anarion80/porcupine/images/porcupine_4thumb_keys_bottom_plate-back.png

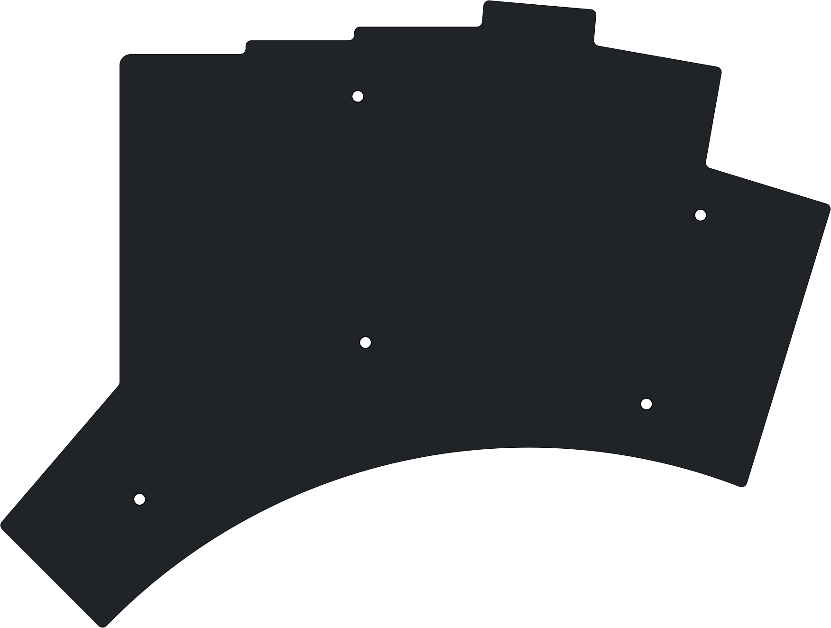
images/porcupine_4thumb_keys_bottom_plate-back.png
