anarion80/porcupine/images/porcupine_6x3_bottom_plate-back.png

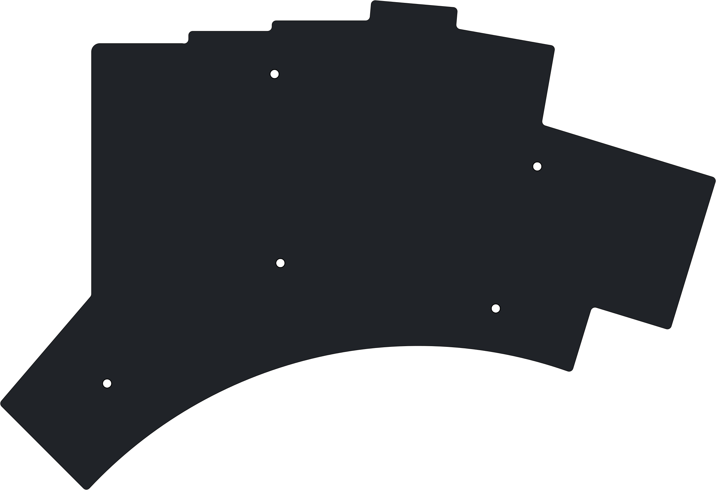
images/porcupine_6x3_bottom_plate-back.png
