anarion80/porcupine/images/porcupine_6x3_top_plate-back.png

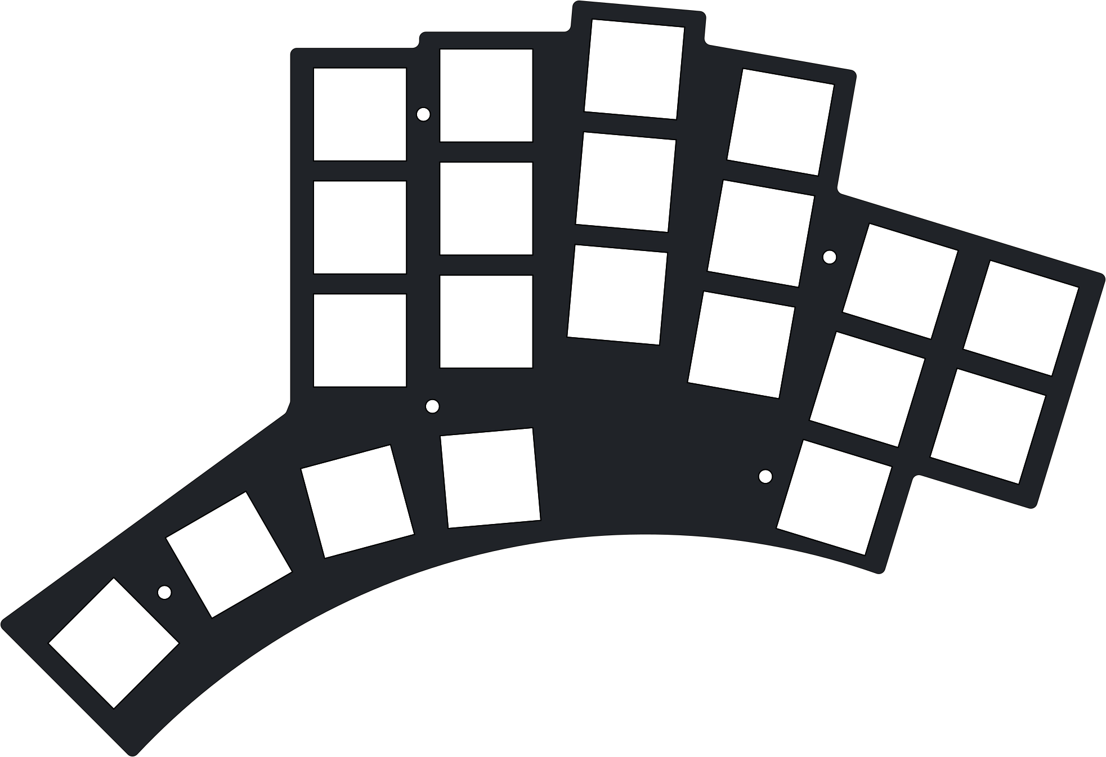
images/porcupine_6x3_top_plate-back.png
