anarion80/porcupine/images/porcupine_bottom_plate-back.png

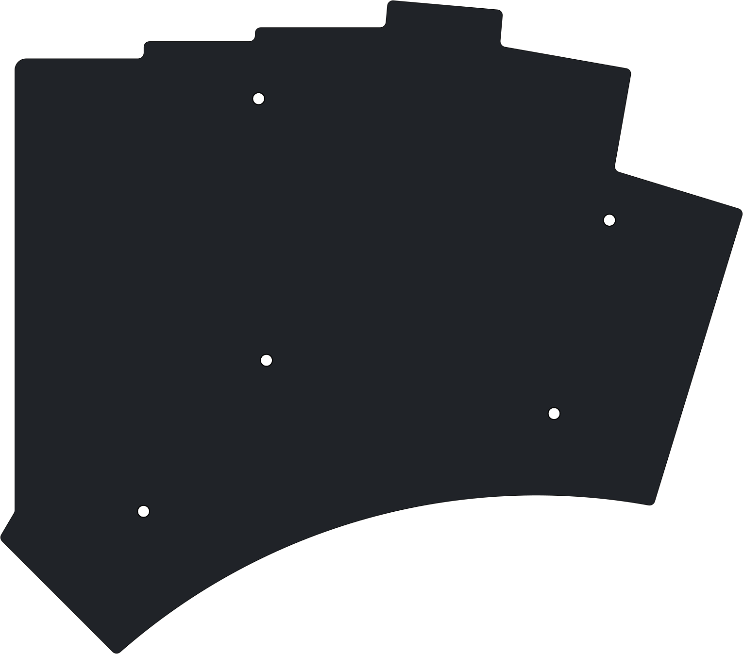
images/porcupine_bottom_plate-back.png
