anarion80/porcupine/images/porcupine_routed-front.png

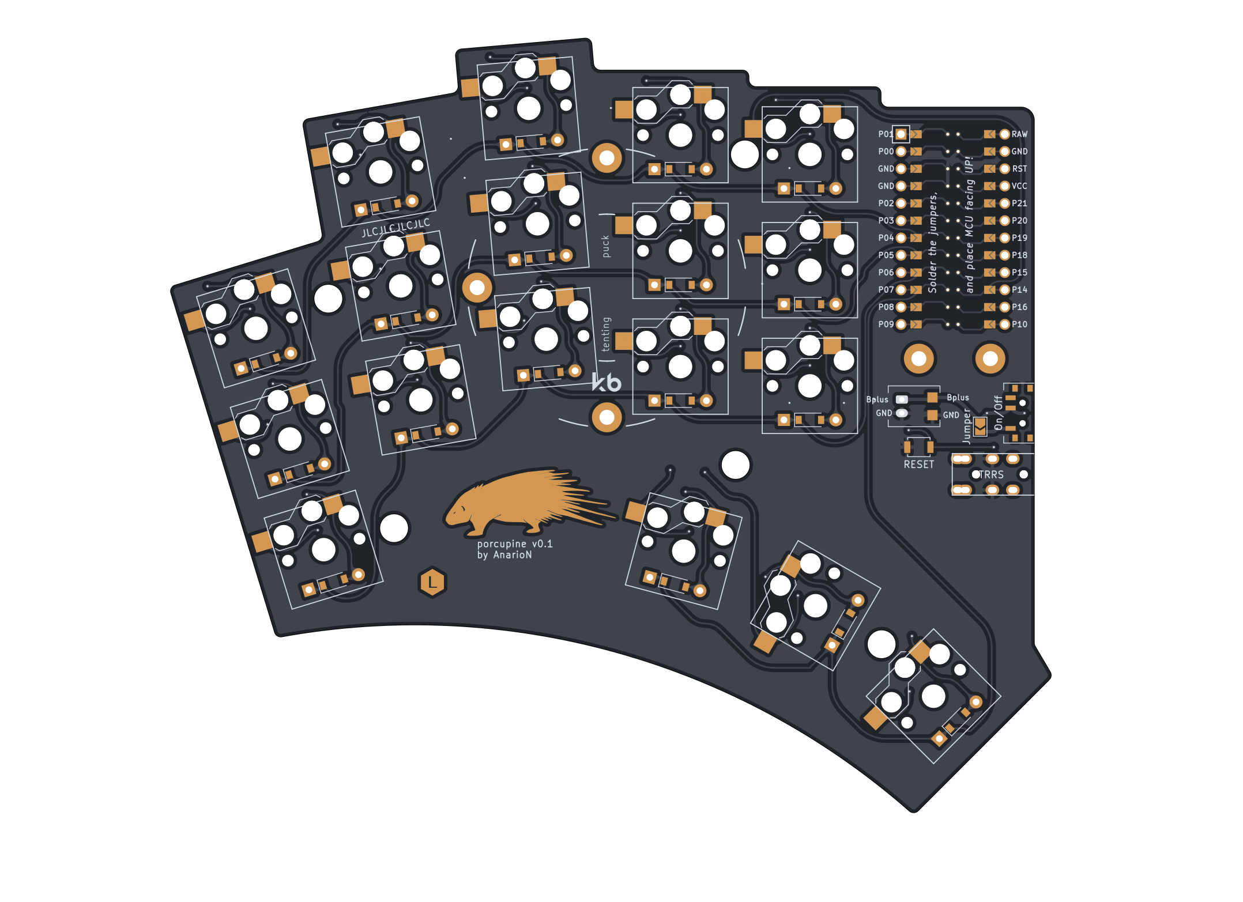
images/porcupine_routed-front.png
