anarion80/porcupine/images/porcupine_top_plate-front.png

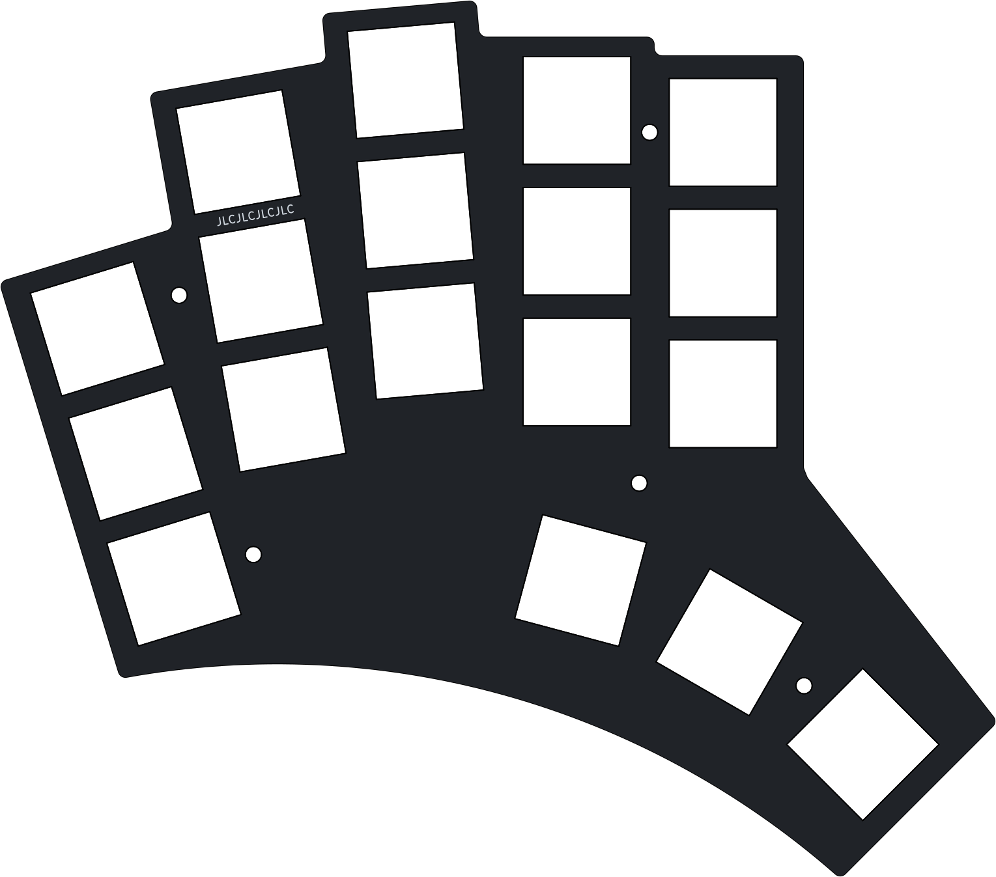
images/porcupine_top_plate-front.png
