anarion80/porcupine/3dmodels/ergogen/CON_SM04B-SRSS-TB.step

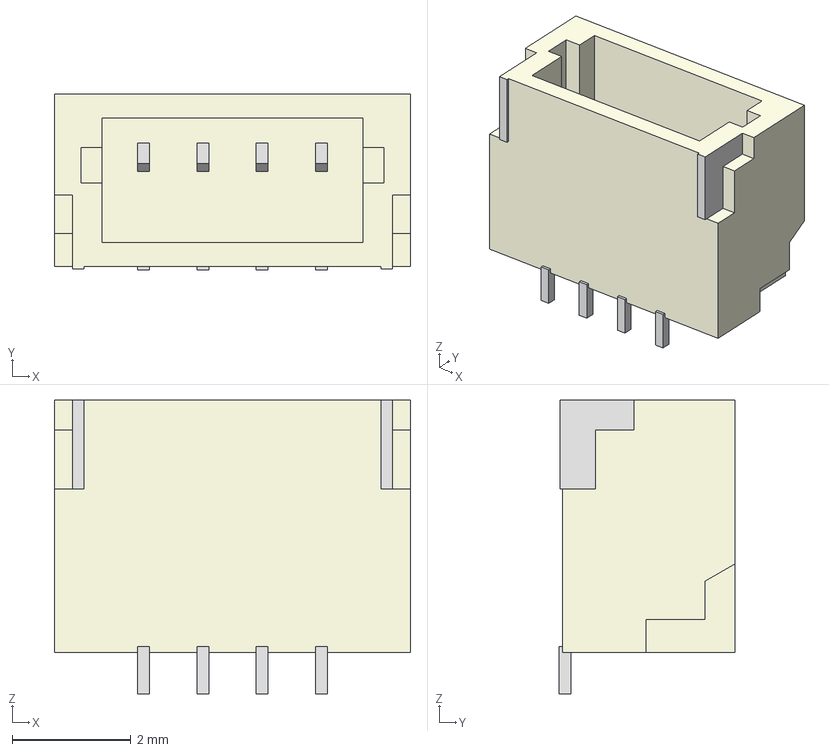
[picture p36: CAD file, 2023-01-22]
3dmodels/ergogen/CON_SM04B-SRSS-TB.step
6.00 x 2.96 x 4.95 mm
