anarion80/porcupine/3dmodels/ergogen/MBK_Keycap_-_1.5u.step

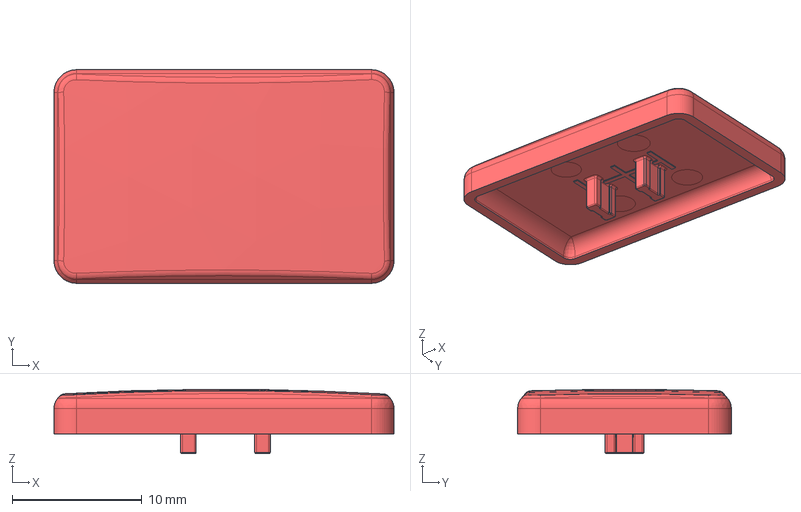
[picture p37: CAD file, 2023-01-22]
3dmodels/ergogen/MBK_Keycap_-_1.5u.step
26.2 x 16.4 x 4.94 mm
