anarion80/porcupine/3dmodels/ergogen/CON_SM08B-SRSS-TB.step

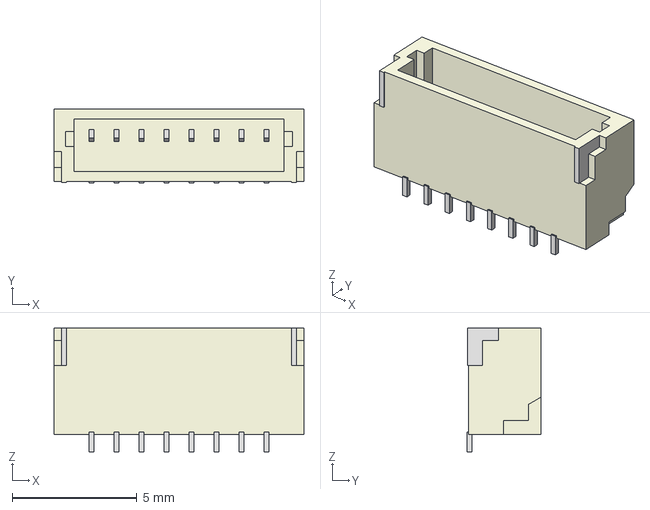
[picture p38: CAD file, 2023-01-22]
3dmodels/ergogen/CON_SM08B-SRSS-TB.step
10.0 x 2.96 x 4.95 mm
