anarion80/porcupine/3dmodels/ergogen/Switch_ESP3020.step

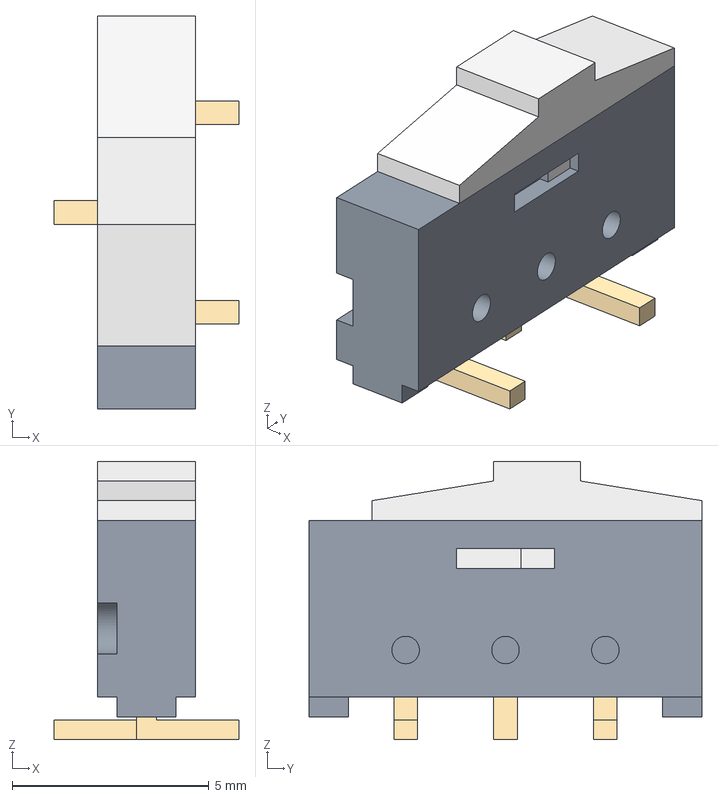
[picture p40: CAD file, 2023-01-22]
3dmodels/ergogen/Switch_ESP3020.step
4.70 x 10.0 x 7.08 mm
