anarion80/porcupine/3dmodels/ergogen/ROT_EC11E.step

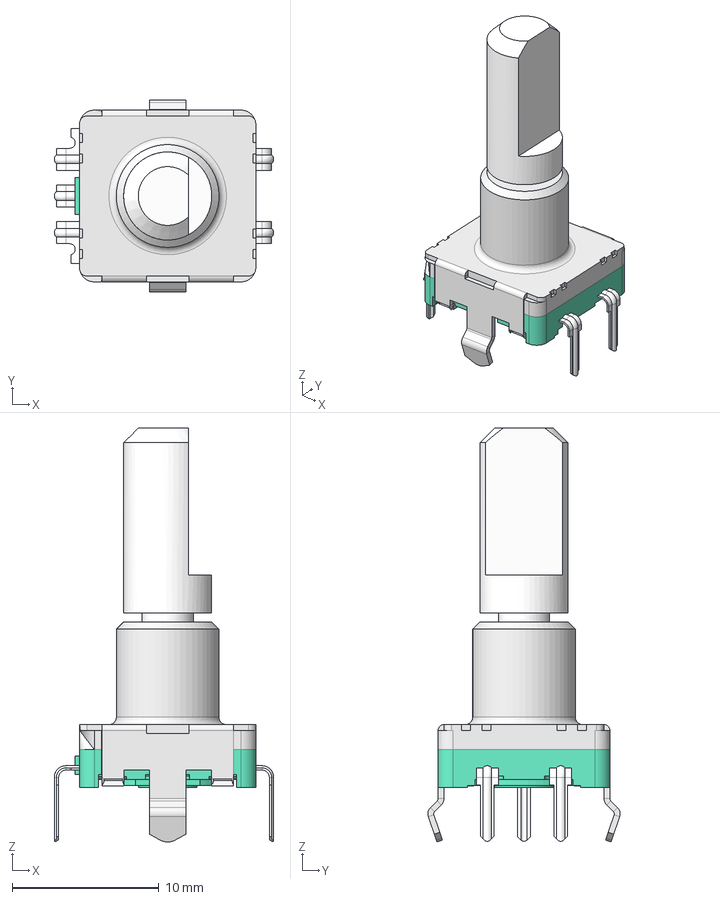
[picture p41: CAD file, 2023-01-22]
3dmodels/ergogen/ROT_EC11E.step
14.9 x 13.1 x 28.2 mm
