anarion80/porcupine/3dmodels/ergogen/Fuse_1206.step

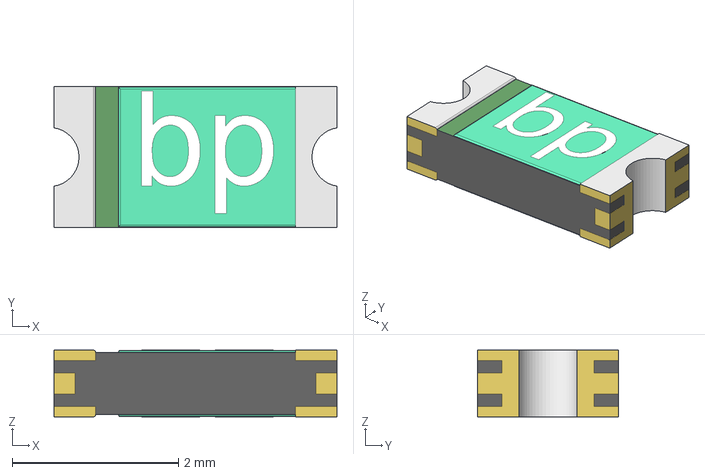
[picture p42: CAD file, 2023-01-22]
3dmodels/ergogen/Fuse_1206.step
3.40 x 1.70 x 0.8 mm
