anarion80/porcupine/3dmodels/ergogen/CON_SM06B-SRSS-TB.step

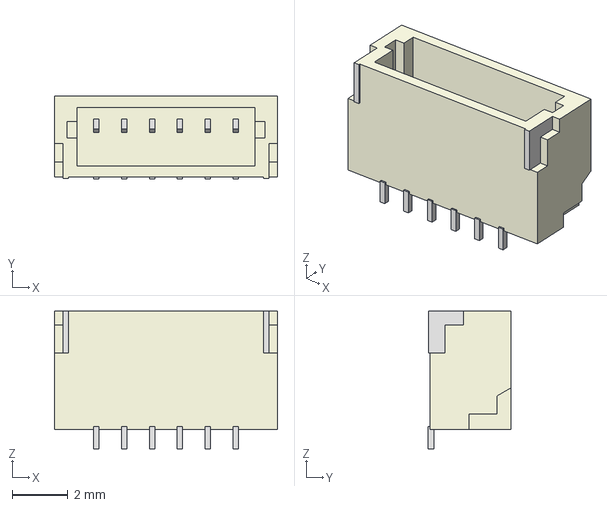
[picture p43: CAD file, 2023-01-22]
3dmodels/ergogen/CON_SM06B-SRSS-TB.step
8.00 x 2.96 x 4.95 mm
