anarion80/porcupine/3dmodels/ergogen/Stabilizer_Cherry_MX_7u.stp

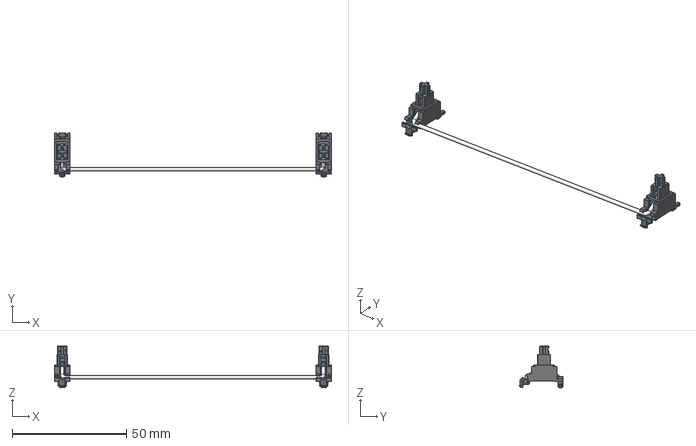
[picture p44: CAD file, 2023-01-22]
3dmodels/ergogen/Stabilizer_Cherry_MX_7u.stp
121.1 x 19.2 x 18.3 mm
