anarion80/porcupine/3dmodels/ergogen/Stabilizer_Cherry_MX_8u.stp

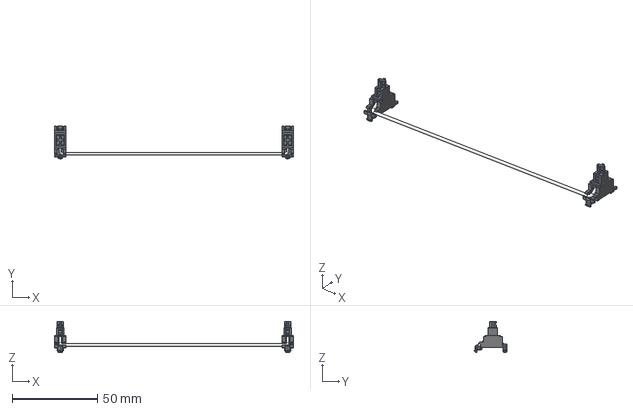
[picture p45: CAD file, 2023-01-22]
3dmodels/ergogen/Stabilizer_Cherry_MX_8u.stp
140.1 x 19.2 x 18.3 mm
