anarion80/porcupine/3dmodels/ergogen/PG1350-socket.STEP

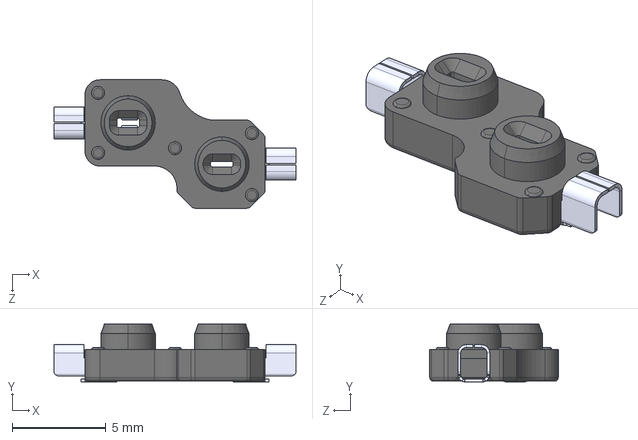
[picture p46: CAD file, 2023-01-22]
3dmodels/ergogen/PG1350-socket.STEP
12.9 x 3.09 x 6.85 mm
pin x 2
socket
