anarion80/porcupine/3dmodels/ergogen/S2B-PH-K-S.step

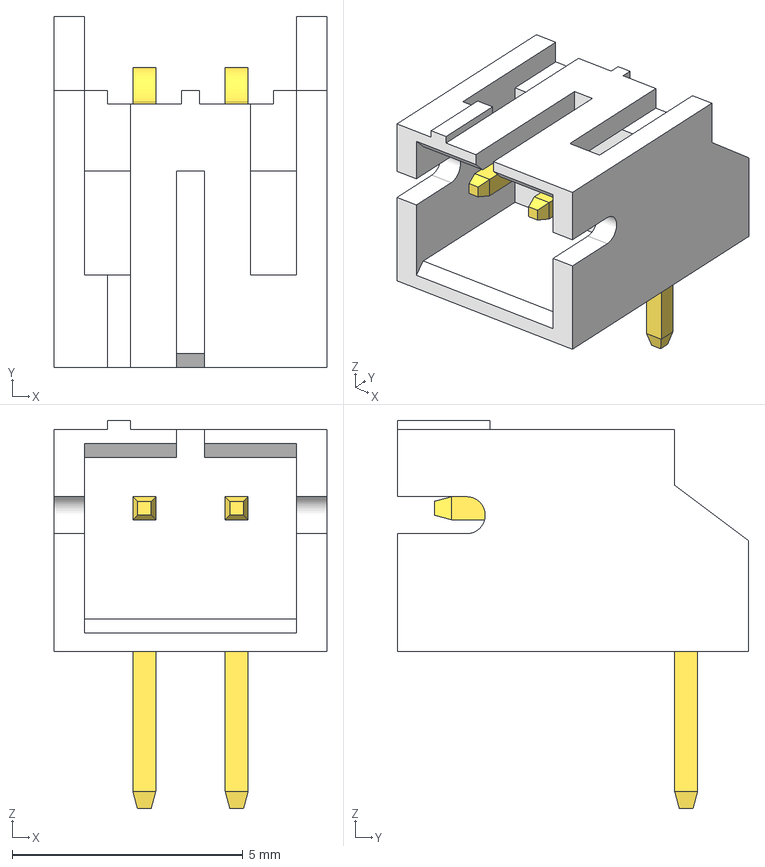
[picture p47: CAD file, 2023-01-22]
3dmodels/ergogen/S2B-PH-K-S.step
5.90 x 7.60 x 8.40 mm
