anarion80/porcupine/3dmodels/ergogen/Stabilizer_Cherry_MX_2u.stp

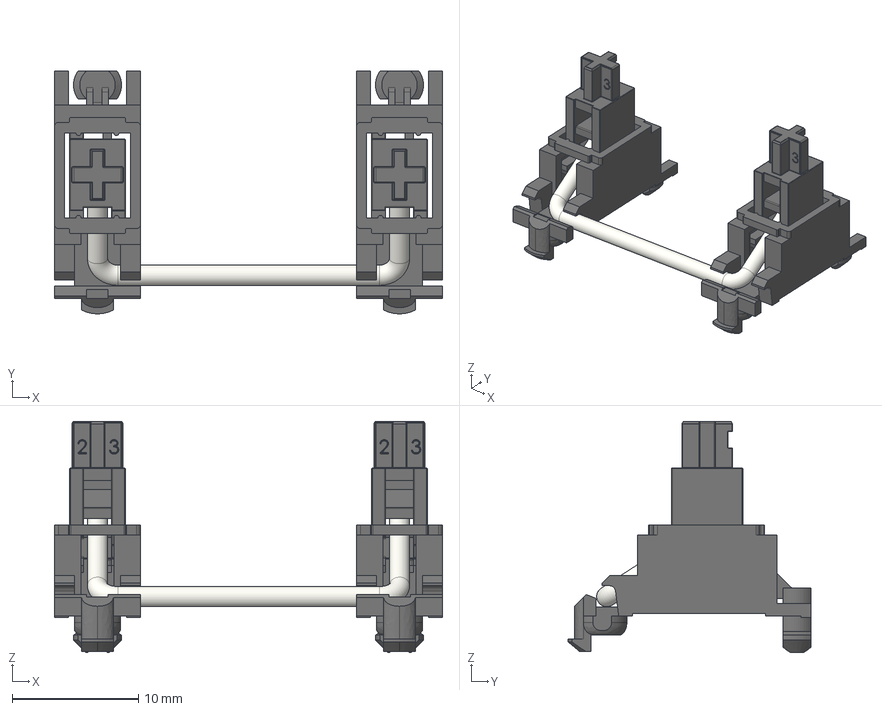
[picture p48: CAD file, 2023-01-22]
3dmodels/ergogen/Stabilizer_Cherry_MX_2u.stp
30.7 x 19.2 x 18.3 mm
