anarion80/porcupine/3dmodels/ergogen/D_SOD-123.step

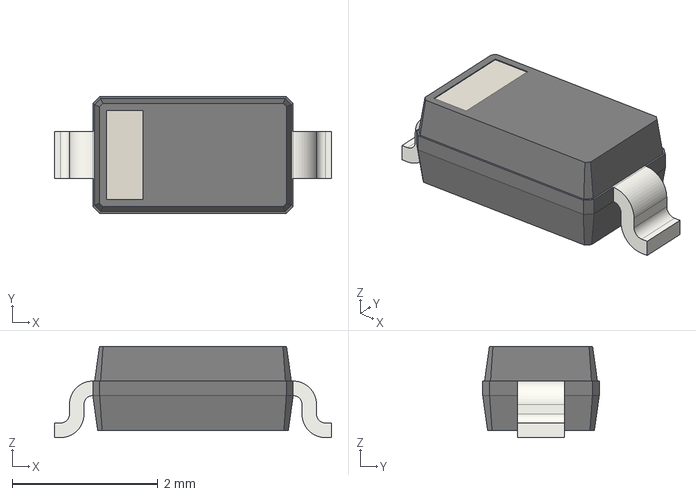
[picture p49: CAD file, 2023-01-22]
3dmodels/ergogen/D_SOD-123.step
3.80 x 1.60 x 1.25 mm
