anarion80/porcupine/3dmodels/ergogen/LED_SK6812MINI-E.step

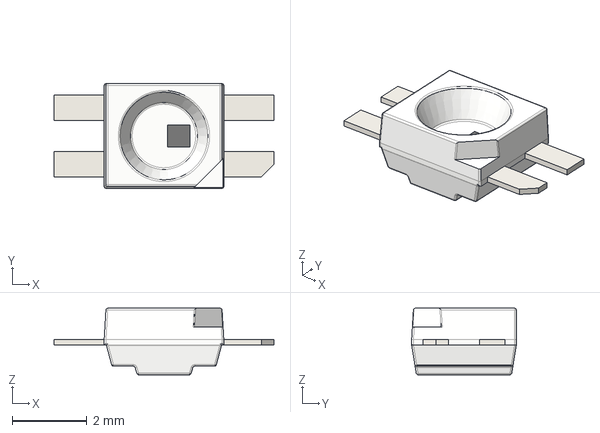
[picture p50: CAD file, 2023-01-22]
3dmodels/ergogen/LED_SK6812MINI-E.step
5.88 x 2.80 x 1.78 mm
