anarion80/porcupine/3dmodels/ergogen/Stabilizer_Cherry_MX_3u.stp

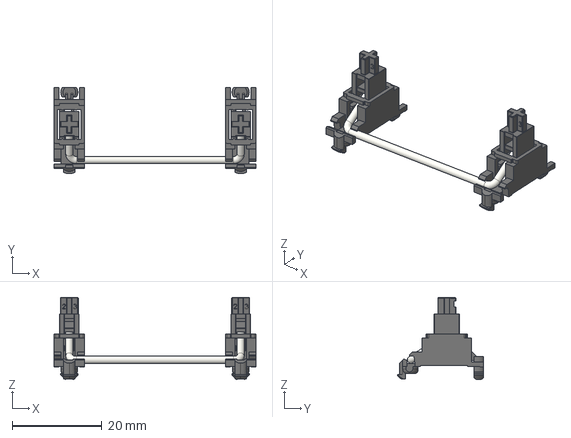
[picture p51: CAD file, 2023-01-22]
3dmodels/ergogen/Stabilizer_Cherry_MX_3u.stp
44.9 x 19.2 x 18.3 mm
