anarion80/porcupine/3dmodels/ergogen/MBK_Keycap_-_2u.step

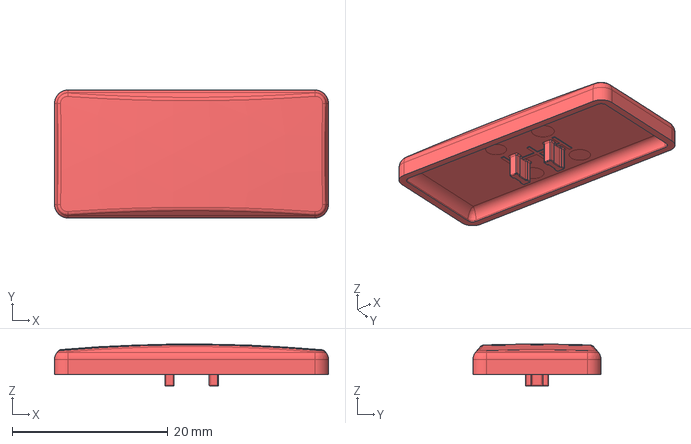
[picture p52: CAD file, 2023-01-22]
3dmodels/ergogen/MBK_Keycap_-_2u.step
35.2 x 16.4 x 5.38 mm
