anarion80/porcupine/3dmodels/ergogen/CON_Kailh_HS.step

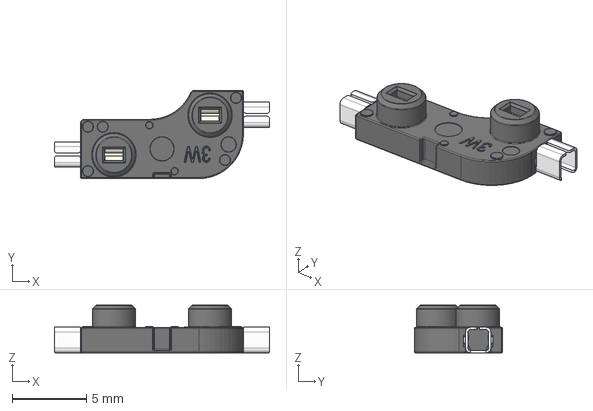
[picture p53: CAD file, 2023-01-22]
3dmodels/ergogen/CON_Kailh_HS.step
14.5 x 5.95 x 3.22 mm
