anarion80/porcupine/3dmodels/ergogen/Stabilizer_Cherry_MX_6u.stp

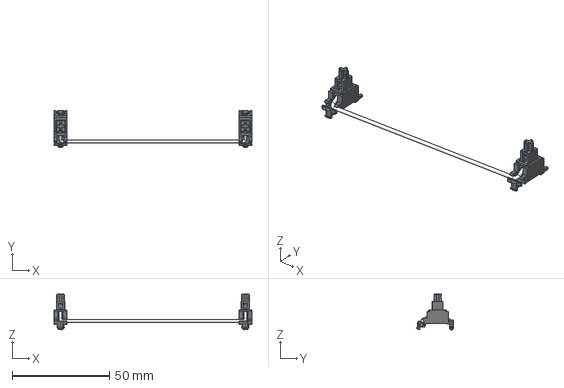
[picture p54: CAD file, 2023-01-22]
3dmodels/ergogen/Stabilizer_Cherry_MX_6u.stp
102.1 x 19.2 x 18.3 mm
