anarion80/porcupine/3dmodels/ergogen/Stabilizer_Cherry_MX_6_25u.stp

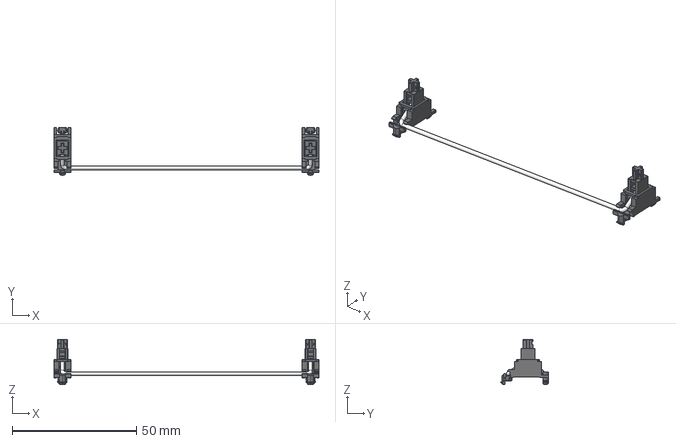
[picture p55: CAD file, 2023-01-22]
3dmodels/ergogen/Stabilizer_Cherry_MX_6_25u.stp
106.8 x 19.2 x 18.3 mm
